Express1/tftlcdClock/pictures/IMG_20191129_123751-0.jpg

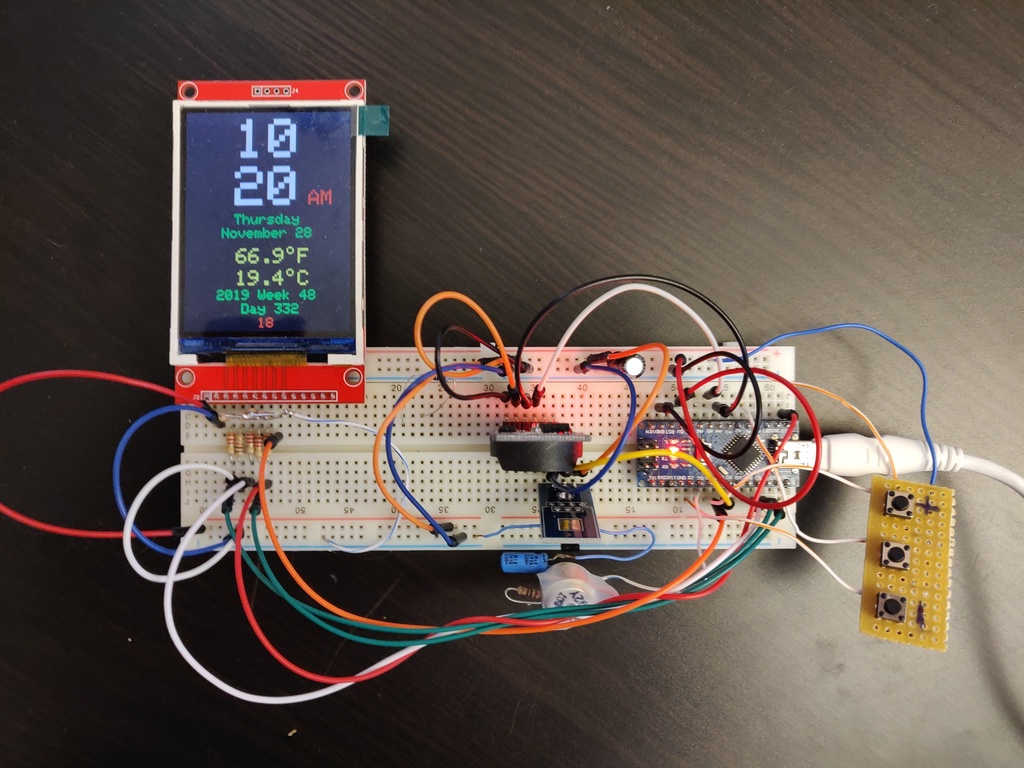
pictures/IMG_20191129_123751-0.jpg
