Express1/tftlcdClock/pictures/IMG_20191129_123751-1.jpg

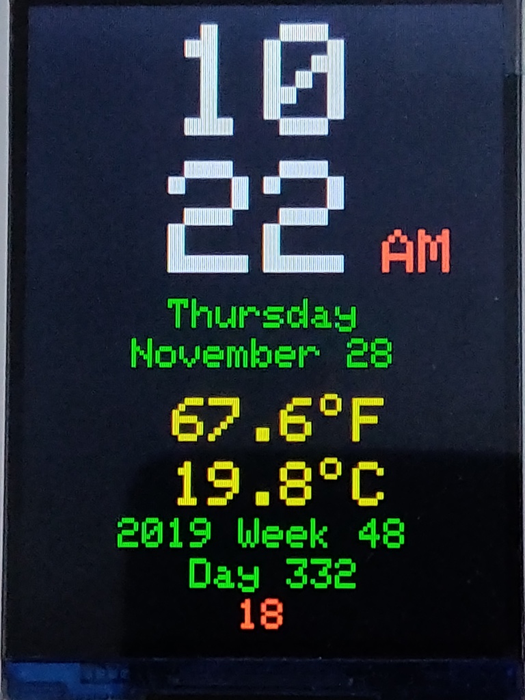
pictures/IMG_20191129_123751-1.jpg
